djordje200179/Niski/Hardware/CPU/AlignmentChecker.sv

module cpu_alignment_checker (
	input [1:0] addr_offset,
	input [3:0] mask,

	output logic overflow
);
	always_comb begin
		overflow = 0;

		unique case (addr_offset)
		0: begin
			overflow = 0;
		end
		1: begin
			if (mask[3])
				overflow = 1;
		end
		2: begin
			if (|mask[3:2])
				overflow = 1;
		end
		3: begin
			if (|mask[3:1])
				overflow = 1;
		end
		endcase
	end
endmodule
