djordje200179/Niski/Hardware/Devices/SSDs/Mappers/Digit.sv

module ssds_digit_mapper (
	input [3:0] digit,
	output logic [6:0] segments
);
	always_comb begin
		unique case (digit)
		4'h0: segments = 7'b0111111;
		4'h1: segments = 7'b0000110;
		4'h2: segments = 7'b1011011;
		4'h3: segments = 7'b1001111;
		4'h4: segments = 7'b1100110;
		4'h5: segments = 7'b1101101;
		4'h6: segments = 7'b1111101;
		4'h7: segments = 7'b0000111;
		4'h8: segments = 7'b1111111;
		4'h9: segments = 7'b1101111;
		4'ha: segments = 7'b1110111;
		4'hb: segments = 7'b1111100;
		4'hc: segments = 7'b0111001;
		4'hd: segments = 7'b1011110;
		4'he: segments = 7'b1111001;
		4'hf: segments = 7'b1110001;
		endcase
	end
endmodule
