djordje200179/Niski/Hardware/Tests/NiskiDUT.v

// Copyright (C) 2023  Intel Corporation. All rights reserved.
// Your use of Intel Corporation's design tools, logic functions 
// and other software and tools, and any partner logic 
// functions, and any output files from any of the foregoing 
// (including device programming or simulation files), and any 
// associated documentation or information are expressly subject 
// to the terms and conditions of the Intel Program License 
// Subscription Agreement, the Intel Quartus Prime License Agreement,
// the Intel FPGA IP License Agreement, or other applicable license
// agreement, including, without limitation, that your use is for
// the sole purpose of programming logic devices manufactured by
// Intel and sold by Intel or its authorized distributors.  Please
// refer to the applicable agreement for further details, at
// https://fpgasoftware.intel.com/eula.

// PROGRAM		"Quartus Prime"
// VERSION		"Version 23.1std.0 Build 991 11/28/2023 SC Lite Edition"
// CREATED		"Wed Mar  6 10:47:54 2024"

module niski_dut(
	CLK_PIN,
	UART_RX_PIN,
	PS2_CLK_PIN,
	PS2_DATA_PIN,
	IR_PIN,
	BTN_PINS,
	BUZZ_PIN,
	UART_TX_PIN,
	SDRAM_CKE_PIN,
	SDRAM_CLK_PIN,
	SDRAM_CS_PIN,
	SDRAM_RAS_PIN,
	SDRAM_CAS_PIN,
	SDRAM_WE_PIN,
	I2C_SCL_PIN,
	LCD_RS_PIN,
	LCD_RW_PIN,
	LCD_E_PIN,
	I2C_SDA_PIN,
	LCD_DATA_PINS,
	LED_PINS,
	SDRAM_ADDR_PINS,
	SDRAM_BANK_PINS,
	SDRAM_DATA_PINS,
	SDRAM_MASK_PINS,
	SEVSEG_SEG_PINS,
	SEVSEG_SEL_PINS
);


input wire	CLK_PIN;
input wire	UART_RX_PIN;
input wire	PS2_CLK_PIN;
input wire	PS2_DATA_PIN;
input wire	IR_PIN;
input wire	[4:0] BTN_PINS;
output wire	BUZZ_PIN;
output wire	UART_TX_PIN;
output wire	SDRAM_CKE_PIN;
output wire	SDRAM_CLK_PIN;
output wire	SDRAM_CS_PIN;
output wire	SDRAM_RAS_PIN;
output wire	SDRAM_CAS_PIN;
output wire	SDRAM_WE_PIN;
output wire	I2C_SCL_PIN;
output wire	LCD_RS_PIN;
output wire	LCD_RW_PIN;
output wire	LCD_E_PIN;
inout wire	I2C_SDA_PIN;
inout wire	[7:0] LCD_DATA_PINS;
output wire	[3:0] LED_PINS;
output wire	[11:0] SDRAM_ADDR_PINS;
output wire	[1:0] SDRAM_BANK_PINS;
inout wire	[15:0] SDRAM_DATA_PINS;
output wire	[1:0] SDRAM_MASK_PINS;
output wire	[7:0] SEVSEG_SEG_PINS;
output wire	[3:0] SEVSEG_SEL_PINS;

wire	[31:0] addr_bus;
wire	btn_rst;
wire	clk_1_hz;
wire	clk_1_khz;
wire	clk_2_khz;
wire	clk_50_mhz;
wire	clk_i50_mhz;
wire	[31:0] data_bus;
wire	[3:0] data_mask_bus;
wire	ext_intr;
wire	[15:1] ext_irqs;
wire	fc_bus;
wire	rd_bus;
wire	wr_bus;
wire	SYNTHESIZED_WIRE_0;
wire	[6:0] SYNTHESIZED_WIRE_1;
wire	[6:0] SYNTHESIZED_WIRE_2;
wire	[6:0] SYNTHESIZED_WIRE_3;
wire	[6:0] SYNTHESIZED_WIRE_4;
wire	[3:0] SYNTHESIZED_WIRE_5;
wire	SYNTHESIZED_WIRE_6;
wire	SYNTHESIZED_WIRE_7;
wire	SYNTHESIZED_WIRE_8;
wire	SYNTHESIZED_WIRE_9;
wire	SYNTHESIZED_WIRE_10;
wire	SYNTHESIZED_WIRE_11;
wire	SYNTHESIZED_WIRE_12;
wire	SYNTHESIZED_WIRE_13;
wire	[10:0] SYNTHESIZED_WIRE_14;
wire	SYNTHESIZED_WIRE_15;
wire	SYNTHESIZED_WIRE_16;
wire	[7:0] SYNTHESIZED_WIRE_17;
wire	SYNTHESIZED_WIRE_18;
wire	[11:0] SYNTHESIZED_WIRE_19;
wire	[31:0] SYNTHESIZED_WIRE_20;
wire	[3:0] SYNTHESIZED_WIRE_21;
wire	[31:0] SYNTHESIZED_WIRE_22;
wire	[31:0] SYNTHESIZED_WIRE_23;
wire	SYNTHESIZED_WIRE_24;
wire	SYNTHESIZED_WIRE_25;
wire	SYNTHESIZED_WIRE_26;
wire	SYNTHESIZED_WIRE_27;
wire	[31:0] SYNTHESIZED_WIRE_28;
wire	SYNTHESIZED_WIRE_29;
wire	SYNTHESIZED_WIRE_44;
wire	SYNTHESIZED_WIRE_31;
wire	SYNTHESIZED_WIRE_32;
wire	SYNTHESIZED_WIRE_33;
wire	SYNTHESIZED_WIRE_34;
wire	SYNTHESIZED_WIRE_35;
wire	SYNTHESIZED_WIRE_36;
wire	SYNTHESIZED_WIRE_37;
wire	[31:0] SYNTHESIZED_WIRE_39;
wire	[3:0] SYNTHESIZED_WIRE_40;
wire	[31:0] SYNTHESIZED_WIRE_41;
wire	SYNTHESIZED_WIRE_42;
wire	SYNTHESIZED_WIRE_43;





i2c_controller	b2v_inst(
	.clk(clk_50_mhz),
	.rst(btn_rst),
	.en(1),
	
	
	.data_pin(I2C_SDA_PIN),
	
	
	
	
	.clk_pin(I2C_SCL_PIN)
	
	);



ssds_controller#(1000, 60)	b2v_inst10(
	.clk(clk_1_khz),
	.rst(btn_rst),
	.en(SYNTHESIZED_WIRE_0),
	.digit_0(SYNTHESIZED_WIRE_1),
	.digit_1(SYNTHESIZED_WIRE_2),
	.digit_2(SYNTHESIZED_WIRE_3),
	.digit_3(SYNTHESIZED_WIRE_4),
	.dots(SYNTHESIZED_WIRE_5),
	.segment_pins(SEVSEG_SEG_PINS),
	.select_pins(SEVSEG_SEL_PINS));


buzzer_bus_interface#(32'b01110000000000000000000000010000)	b2v_inst11(
	.clk(clk_50_mhz),
	.rst(btn_rst),
	.rd_bus(rd_bus),
	.wr_bus(wr_bus),
	.addr_bus(addr_bus),
	.data_bus(data_bus),
	.data_mask_bus(data_mask_bus),
	.ctrl_en(SYNTHESIZED_WIRE_42),
	.ctrl_buzz(SYNTHESIZED_WIRE_43),
	.fc_bus(fc_bus)
	);


leds_controller	b2v_inst12(
	.en(SYNTHESIZED_WIRE_6),
	.led0(SYNTHESIZED_WIRE_7),
	.led1(SYNTHESIZED_WIRE_8),
	.led2(SYNTHESIZED_WIRE_9),
	.led3(SYNTHESIZED_WIRE_10),
	.led_pins(LED_PINS));


rising_edge_detector	b2v_inst13(
	.clk(clk_50_mhz),
	.rst(btn_rst),
	.raw_input(clk_1_hz),
	.rising_edge(SYNTHESIZED_WIRE_26));


leds_bus_interface#(32'b01110000000000000000000000000000)	b2v_inst14(
	.clk(clk_50_mhz),
	.rst(btn_rst),
	.rd_bus(rd_bus),
	.wr_bus(wr_bus),
	.addr_bus(addr_bus),
	.data_bus(data_bus),
	.data_mask_bus(data_mask_bus),
	.ctrl_en(SYNTHESIZED_WIRE_6),
	.ctrl_led0(SYNTHESIZED_WIRE_7),
	.ctrl_led1(SYNTHESIZED_WIRE_8),
	.ctrl_led2(SYNTHESIZED_WIRE_9),
	.ctrl_led3(SYNTHESIZED_WIRE_10),
	.fc_bus(fc_bus)
	);


lcd_bus_interface	b2v_inst15(
	.clk(clk_50_mhz),
	.rst(btn_rst),
	.ctrl_data_ack(SYNTHESIZED_WIRE_11),
	.rd_bus(rd_bus),
	.wr_bus(wr_bus),
	.addr_bus(addr_bus),
	.data_bus(data_bus),
	.data_mask_bus(data_mask_bus),
	.ctrl_data_is_cmd(SYNTHESIZED_WIRE_15),
	.ctrl_data_req(SYNTHESIZED_WIRE_16),
	.fc_bus(fc_bus),
	.ctrl_data(SYNTHESIZED_WIRE_17)
	);
	defparam	b2v_inst15.START_ADDR = 32'b01110000000000000000000000110000;


bus_arbitrator	b2v_inst16(
	.clk(clk_50_mhz),
	.rst(btn_rst),
	.cpu_req(SYNTHESIZED_WIRE_12),
	.dma_req(SYNTHESIZED_WIRE_13),
	.cpu_grant(SYNTHESIZED_WIRE_35),
	.dma_grant(SYNTHESIZED_WIRE_29),
	.wr_bus(wr_bus),
	.rd_bus(rd_bus),
	.fc_bus(fc_bus),
	.addr_bus(addr_bus),
	.data_bus(data_bus),
	.data_mask_bus(data_mask_bus));


PLL	b2v_inst17(
	.inclk0(clk_50_mhz),
	.areset(btn_rst),
	
	.c1(clk_2_khz));


rom#(11, "../../Software/out/rom.mem")	b2v_inst18(
	.clk(clk_50_mhz),
	.addr(SYNTHESIZED_WIRE_14),
	.data_out(SYNTHESIZED_WIRE_23));


lcd_controller	b2v_inst19(
	.clk(clk_50_mhz),
	.rst(btn_rst),
	.data_is_cmd(SYNTHESIZED_WIRE_15),
	.data_req(SYNTHESIZED_WIRE_16),
	.data_in(SYNTHESIZED_WIRE_17),
	.data_pins(LCD_DATA_PINS),
	.rs_pin(LCD_RS_PIN),
	.e_pin(LCD_E_PIN),
	.rw_pin(LCD_RW_PIN),
	.data_ack(SYNTHESIZED_WIRE_11)
	);



ram#(12, "../../Software/out/ram.mem") 	b2v_inst20(
	.clk(clk_50_mhz),
	.wr(SYNTHESIZED_WIRE_18),
	.addr(SYNTHESIZED_WIRE_19),
	.data_in(SYNTHESIZED_WIRE_20),
	.wr_mask(SYNTHESIZED_WIRE_21),
	.data_out(SYNTHESIZED_WIRE_22));


memory_bus_interface#(12, 32'b01010000000000000000000000000000) b2v_inst21(
	.clk(clk_50_mhz),
	.rst(btn_rst),
	.wr_bus(wr_bus),
	.rd_bus(rd_bus),
	.addr_bus(addr_bus),
	.data_bus(data_bus),
	.data_mask_bus(data_mask_bus),
	.mem_data_out(SYNTHESIZED_WIRE_22),
	.mem_wr(SYNTHESIZED_WIRE_18),
	.fc_bus(fc_bus),
	
	.mem_addr(SYNTHESIZED_WIRE_19),
	.mem_data_in(SYNTHESIZED_WIRE_20),
	.mem_wr_mask(SYNTHESIZED_WIRE_21));


memory_bus_interface#(11, 32'b01000000000000000000000000000000)	b2v_inst22(
	.clk(clk_50_mhz),
	.rst(btn_rst),
	.wr_bus(wr_bus),
	.rd_bus(rd_bus),
	.addr_bus(addr_bus),
	.data_bus(data_bus),
	.data_mask_bus(data_mask_bus),
	.mem_data_out(SYNTHESIZED_WIRE_23),
	
	.fc_bus(fc_bus),
	
	.mem_addr(SYNTHESIZED_WIRE_14)
	
	);


watchdog	b2v_inst23(
	.clk(clk_50_mhz),
	.rst(btn_rst),
	.rd_bus(rd_bus),
	.wr_bus(wr_bus),
	.fc_bus(fc_bus),
	.access_timeout(SYNTHESIZED_WIRE_44));
	defparam	b2v_inst23.ALLOWED_SECONDS = 0.01;


low_freq_clock	b2v_inst24(
	.clk_2_khz(clk_2_khz),
	.rst(btn_rst),
	.clk_1_khz(clk_1_khz),
	.clk_1_hz(clk_1_hz));


cpu	b2v_inst25(
	.clk(clk_50_mhz),
	.rst(btn_rst),
	.ma_done(SYNTHESIZED_WIRE_24),
	.ma_timeout(SYNTHESIZED_WIRE_25),
	.timer_intr(SYNTHESIZED_WIRE_26),
	.ext_intr(SYNTHESIZED_WIRE_27),
	.ma_data_in(SYNTHESIZED_WIRE_28),
	.ma_rd_req(SYNTHESIZED_WIRE_37),
	.ma_wr_req(SYNTHESIZED_WIRE_36),
	.ma_addr(SYNTHESIZED_WIRE_39),
	.ma_data_mask(SYNTHESIZED_WIRE_40),
	.ma_data_out(SYNTHESIZED_WIRE_41));
	defparam	b2v_inst25.EXEC_START_ADDR = 32'b01000000000000000000000000000000;
	defparam	b2v_inst25.MORE_REGISTERS = 1'b0;


dma#(32'b01110000000000000000000001000000)	b2v_inst26(
	.clk(clk_50_mhz),
	.rst(btn_rst),
	.bus_grant(SYNTHESIZED_WIRE_29),
	.watchdog(SYNTHESIZED_WIRE_44),
	.rd_bus(rd_bus),
	.wr_bus(wr_bus),
	.fc_bus(fc_bus),
	.addr_bus(addr_bus),
	.data_bus(data_bus),
	.data_mask_bus(data_mask_bus),
	.bus_req(SYNTHESIZED_WIRE_13)
	
	
	
	
	
	);


plic#(32'b01110000000000000000000001010000, 16)	b2v_inst27(
	.clk(clk_50_mhz),
	.rst(btn_rst),
	.rd_bus(rd_bus),
	.wr_bus(wr_bus),
	.addr_bus(addr_bus),
	.data_bus(data_bus),
	.data_mask_bus(data_mask_bus),
	.irqs(ext_irqs),
	.has_req(ext_intr),
	.fc_bus(fc_bus)
	);


rising_edge_detector	b2v_inst28(
	.clk(clk_50_mhz),
	.rst(btn_rst),
	.raw_input(ext_intr),
	.rising_edge(SYNTHESIZED_WIRE_27));


buttons_bus_interface#(32'b01110000000000000000000001100000)	b2v_inst29(
	.clk(clk_50_mhz),
	.rst(btn_rst),
	.btn_0(SYNTHESIZED_WIRE_31),
	.btn_1(SYNTHESIZED_WIRE_32),
	.btn_2(SYNTHESIZED_WIRE_33),
	.btn_3(SYNTHESIZED_WIRE_34),
	.rd_bus(rd_bus),
	.wr_bus(wr_bus),
	.addr_bus(addr_bus),
	.data_bus(data_bus),
	.data_mask_bus(data_mask_bus),
	.irq_0(ext_irqs[4]),
	.irq_1(ext_irqs[5]),
	.irq_2(ext_irqs[6]),
	.irq_3(ext_irqs[7]),
	.fc_bus(fc_bus)
	);


ps2_keyboard_controller	b2v_inst3(
	.clk(clk_50_mhz),
	.rst(1),
	.en(btn_rst),
	
	.data_pin(PS2_DATA_PIN),
	.clk_pin(PS2_CLK_PIN)
	
	
	);


cpu_bus_interface	b2v_inst31(
	.clk(clk_50_mhz),
	.rst(btn_rst),
	.bus_grant(SYNTHESIZED_WIRE_35),
	.fc_bus(fc_bus),
	.wr_req(SYNTHESIZED_WIRE_36),
	.rd_req(SYNTHESIZED_WIRE_37),
	.watchdog(SYNTHESIZED_WIRE_44),
	.addr(SYNTHESIZED_WIRE_39),
	.data_bus(data_bus),
	.data_mask(SYNTHESIZED_WIRE_40),
	.data_out(SYNTHESIZED_WIRE_41),
	.bus_req(SYNTHESIZED_WIRE_12),
	.rd_bus(rd_bus),
	.wr_bus(wr_bus),
	.done(SYNTHESIZED_WIRE_24),
	.timeout(SYNTHESIZED_WIRE_25),
	.addr_bus(addr_bus),
	
	.data_in(SYNTHESIZED_WIRE_28),
	.data_mask_bus(data_mask_bus));


buttons_controller#(4)	b2v_inst4(
	.clk(clk_1_khz),
	.button_pins(BTN_PINS),
	.btn_0(SYNTHESIZED_WIRE_31),
	.btn_1(SYNTHESIZED_WIRE_32),
	.btn_2(SYNTHESIZED_WIRE_33),
	.btn_3(SYNTHESIZED_WIRE_34),
	.btn_rst(btn_rst));


sdram_controller	b2v_inst5(
	.clk(clk_50_mhz),
	.rst(btn_rst),
	.en(1),
	
	
	
	
	.data_pins(SDRAM_DATA_PINS),
	.cke_pin(SDRAM_CKE_PIN),
	.clk_pin(SDRAM_CLK_PIN),
	.cs_pin(SDRAM_CS_PIN),
	.ras_pin(SDRAM_RAS_PIN),
	.cas_pin(SDRAM_CAS_PIN),
	.we_pin(SDRAM_WE_PIN),
	
	.addr_pins(SDRAM_ADDR_PINS),
	.bank_pins(SDRAM_BANK_PINS),
	
	
	.mask_pins(SDRAM_MASK_PINS));


uart_controller	b2v_inst6(
	.clk(clk_50_mhz),
	.rst(btn_rst),
	.en(1),
	
	
	.rx_pin(UART_RX_PIN),
	
	
	
	.tx_pin(UART_TX_PIN)
	);
	defparam	b2v_inst6.BAUD_RATE = 9600;


ssds_bus_interface#(32'b01110000000000000000000000100000)	b2v_inst7(
	.clk(clk_50_mhz),
	.rst(btn_rst),
	.rd_bus(rd_bus),
	.wr_bus(wr_bus),
	.addr_bus(addr_bus),
	.data_bus(data_bus),
	.data_mask_bus(data_mask_bus),
	.ctrl_en(SYNTHESIZED_WIRE_0),
	.fc_bus(fc_bus),
	.ctrl_digit_0(SYNTHESIZED_WIRE_1),
	.ctrl_digit_1(SYNTHESIZED_WIRE_2),
	.ctrl_digit_2(SYNTHESIZED_WIRE_3),
	.ctrl_digit_3(SYNTHESIZED_WIRE_4),
	.ctrl_dots(SYNTHESIZED_WIRE_5)
	);


ir_controller	b2v_inst8(
	.clk(clk_50_mhz),
	.rst(btn_rst),
	.en(1),
	
	.data_pin(IR_PIN)
	
	);


buzzer_controller	b2v_inst9(
	.en(SYNTHESIZED_WIRE_42),
	.buzz(SYNTHESIZED_WIRE_43),
	.buzzer_pin(BUZZ_PIN));

assign	clk_50_mhz = CLK_PIN;

endmodule
