djordje200179/Niski/Hardware/Tests/Niski.sv

`timescale 1 ps / 1 ps

module niski_tb;
	reg clk = 0;
	always #20 clk = ~clk;

	reg clk_1_hz = 1'b0;
	always #100000 clk_1_hz = ~clk_1_hz;

	reg btn = 1'b0;

	reg rst = 1'b0;
	initial begin
		#2 rst = 1'b1;
		#2 rst = 1'b0;
		$stop;
	end

	wire [4:0] btns = {~rst, ~btn, 3'b111};
	wire [3:0] leds;
	wire [6:0] ssds_segments;
	wire [3:0] ssds_select;
	wire lcd_rs, lcd_rw, lcd_e;
	wire [7:0] lcd_data;
	

	`include "NiskiDUT.v"
	niski_dut dut (
		.CLK_PIN(clk), 

		.BTN_PINS(btns),
		.LED_PINS(leds),

		.SEVSEG_SEG_PINS(ssds_segments),
		.SEVSEG_SEL_PINS(ssds_select),

		.LCD_RS_PIN(lcd_rs),
		.LCD_RW_PIN(lcd_rw),
		.LCD_E_PIN(lcd_e),
		.LCD_DATA_PINS(lcd_data)
	);

	initial begin
		#100000;
		btn = 1'b1;
		#200;
		btn = 1'b0;
		#10000;
		$stop;
	end

	always @(dut.b2v_inst25.pc) $strobe("PC: %h, at %t", dut.b2v_inst25.pc, $time);

	string register_names[32] = {
		"zero",
		"ra", "sp",
		"gp", "tp",
		"t0", "t1", "t2",
		"s0", "s1",
		"a0", "a1", "a2", "a3", "a4", "a5", "a6", "a7",
		"s2", "s3", "s4", "s5", "s6", "s7", "s8", "s9", "s10", "s11",
		"t3", "t4", "t5", "t6"
	};
endmodule
